jmoonware/anemometer/docs/glue_board.kicad_sch

## KiCad design docs/glue_board.kicad_sch (2025-12-09)

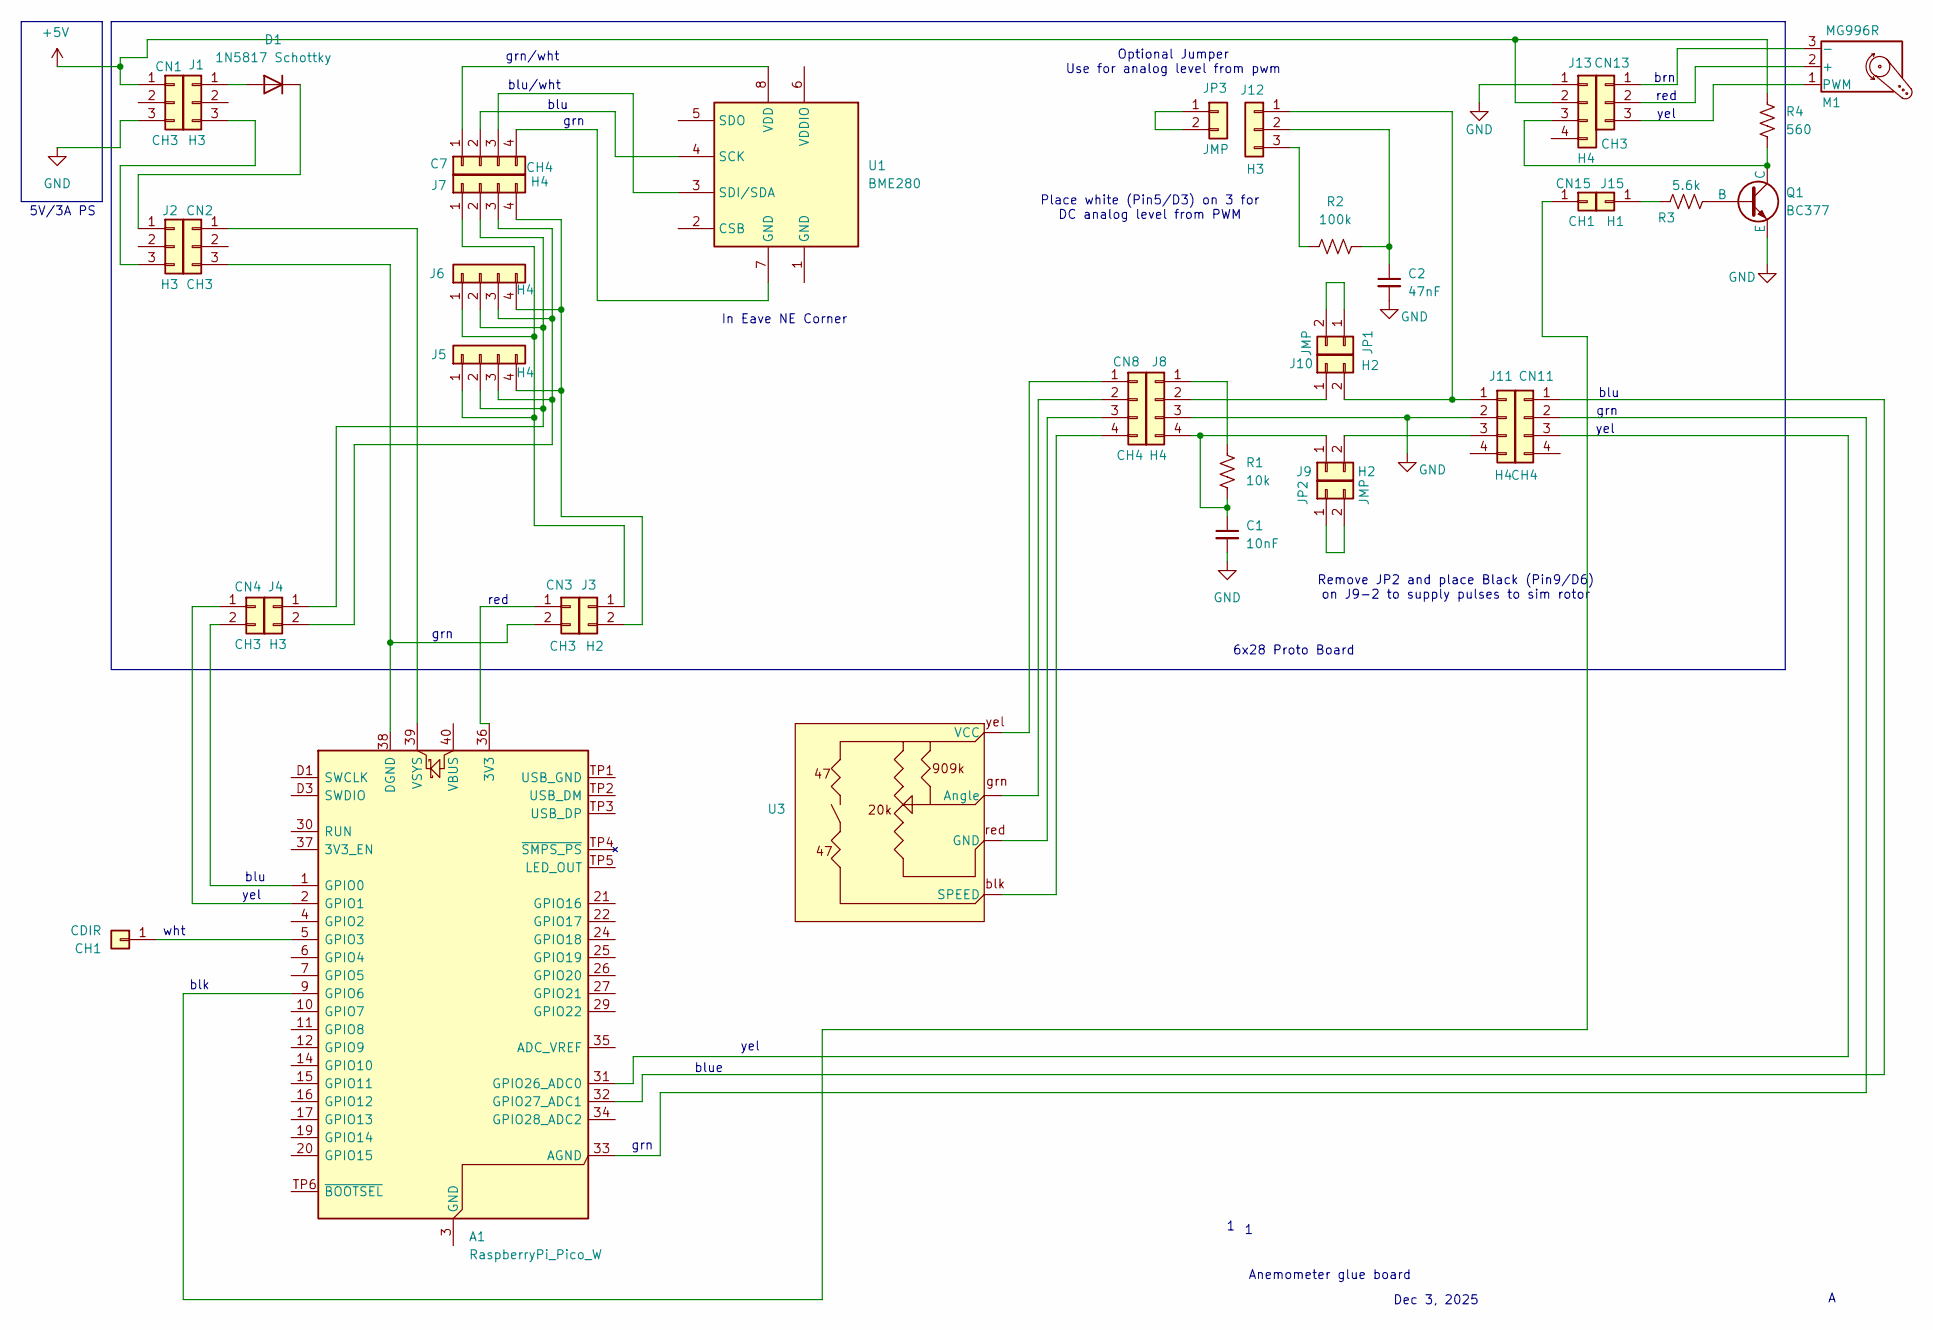
[picture p2: schematic glue_board.kicad_sch]

Parts:
A1: RaspberryPi_Pico_W; RaspberryPi_Pico_W_SMD
C1: 10nF
C2: 47nF
C7: CH4
CDIR: CH1
CN1, CN2, CN3, CN4, CN13: CH3
CN8, CN11: CH4
CN15: CH1
D1: 1N5817 Schottky; D_SOD-523
J1, J2, J4, J12: H3
J3, J9, J10: H2
J5, J6, J7, J8, J11, J13: H4
J15: H1
JP1, JP2, JP3: JMP
M1: MG996R
Q1: BC377
R1: 10k
R2: 100k
R3: 5.6k
R4: 560
U1: BME280; Bosch_LGA-8_2.5x2.5mm_P0.65mm_ClockwisePinNumbering
U3: (no value)

Connections:
+5V: CN1.1, J13.2, R4.1
GND: C1.2, C2.2, CN1.3, J8.3, J11.2, J13.1, Q1.3 (E)
unnamed: A1.1 (GPIO0), CN4.2
unnamed: A1.2 (GPIO1), CN4.1
unnamed: A1.5 (GPIO3), CDIR.1
unnamed: A1.9 (GPIO6), CN15.1
unnamed: A1.3 (GND), A1.8 (GND), A1.13 (GND), A1.18 (GND), A1.23 (GND), A1.28 (GND), A1.38 (DGND), A1.D2 (GND)
unnamed: A1.31 (GPIO26_ADC0), CN11.3
unnamed: A1.32 (GPIO27_ADC1), CN11.1
unnamed: A1.33 (AGND), CN11.2
unnamed: A1.36 (3V3), CN3.1
unnamed: A1.38 (DGND), CN2.3, CN3.2
unnamed: A1.39 (VSYS), CN2.1
unnamed: C1.1, J8.4, J9.1, R1.2
unnamed: C2.1, J12.2, R2.2
unnamed: C7.1, U1.8 (VDD)
unnamed: C7.2, U1.4 (SCK)
unnamed: C7.3, U1.3 (SDI/SDA)
unnamed: C7.4, U1.7 (GND)
unnamed: CN8.1, U3.
unnamed: CN8.2, U3.
unnamed: CN8.3, U3.
unnamed: CN8.4, U3.
unnamed: CN13.1, M1.3 (-)
unnamed: CN13.2, M1.2 (+)
unnamed: CN13.3, M1.1 (PWM)
unnamed: D1.1 (K), J2.1
unnamed: D1.2 (A), J1.1
unnamed: J1.3, J2.3
unnamed: J3.1, J5.1, J6.1, J7.1
unnamed: J3.2, J5.4, J6.4, J7.4
unnamed: J4.1, J5.2, J6.2, J7.2
unnamed: J4.2, J5.3, J6.3, J7.3
unnamed: J8.1, R1.1
unnamed: J8.2, J10.1
unnamed: J10.2, J11.1, J12.1
unnamed: J9.2, J11.3
unnamed: J12.3, R2.1
unnamed: J13.3, Q1.1 (C), R4.2
unnamed: J15.1, R3.2
unnamed: JP1.1, JP1.2
unnamed: JP2.1, JP2.2
unnamed: JP3.1, JP3.2
unnamed: Q1.2 (B), R3.1

Notes on the sheet:
Remove JP2 and place Black (Pin9/D6) on J9-2 to supply pulses to sim rotor
blu/wht
blu
yel
Anemometer glue board
red
grn
Dec 3, 2025
wht
Place white (Pin5/D3) on 3 for DC analog level from PWM
6x28 Proto Board
brn
5V/3A PS
Optional Jumper Use for analog level from pwm
blue
In Eave NE Corner
blk
grn/wht
